psychogenic/gamepad-pmod/hardware/GamepadPMOD/GamepadPMOD.kicad_sch

## KiCad design hardware/GamepadPMOD/GamepadPMOD.kicad_sch (2026-09-07)

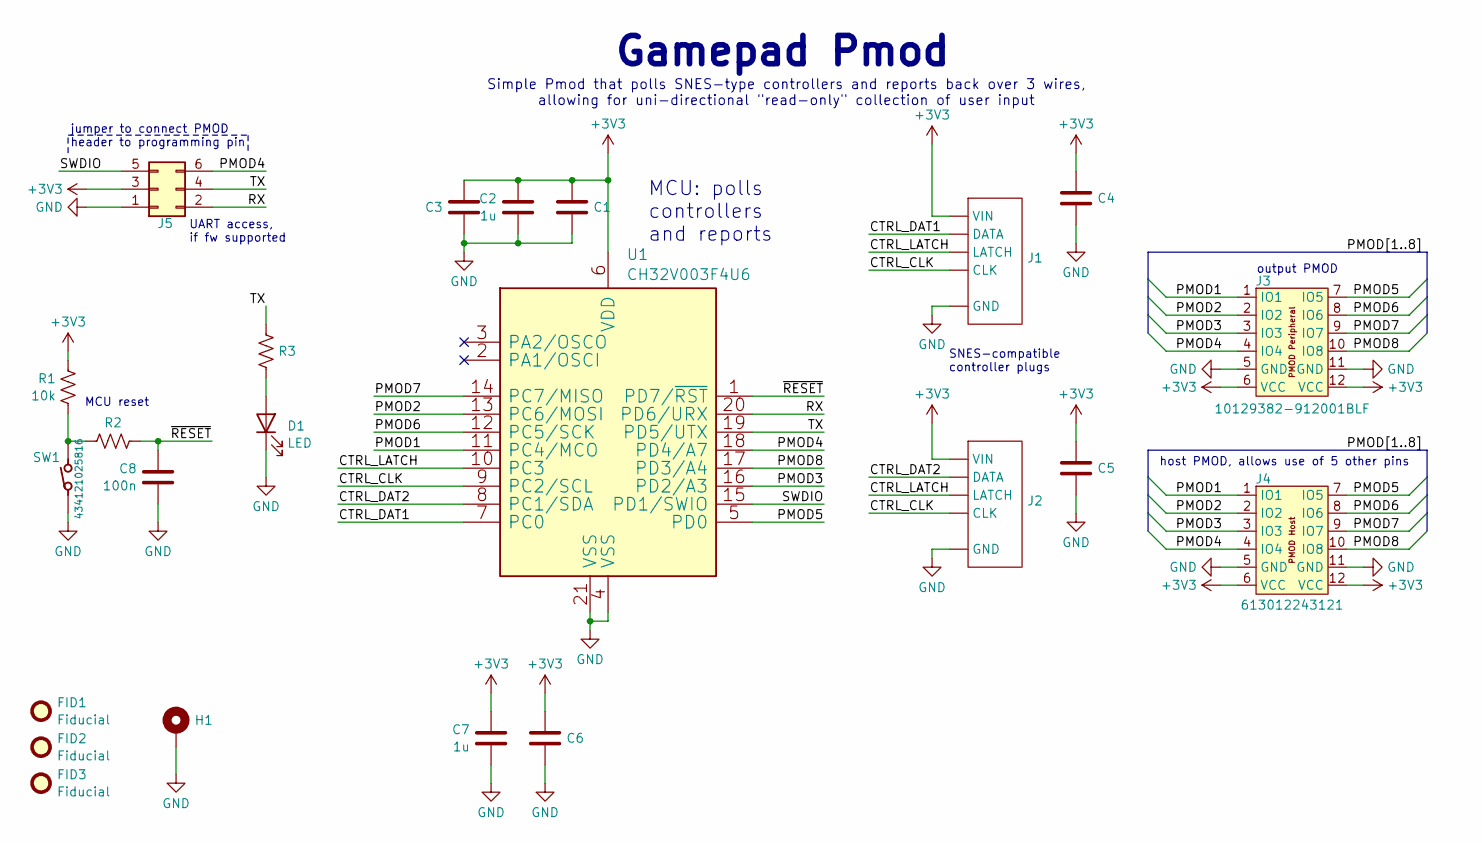
[picture p14: schematic GamepadPMOD.kicad_sch]

Parts:
C1, C4, C5, C6: C_10u_0805_35V; C_0805_2012Metric; MPN CL21A106KOQNNNE; DigikeyPN 490-10514-1-ND
C2, C7: C_1u_0603_50V; C_0603_1608Metric; MPN CL10A105KB8NNNC; DigikeyPN 490-12330-1-ND
C3, C8: C_100n_0402_50V; C_0402_1005Metric; MPN CL05B104KO5NNNC; DigikeyPN 490-13342-1-ND
D1: LED; LED_0603_1608Metric; MPN APT1608SURCK; DigikeyPN 754-1123-1-ND
FID1, FID2, FID3: Fiducial; Fiducial_1mm_Mask2mm
H1: MountingHole_Pad; MountingHole_3.2mm_M3_ISO7380_Pad
J1, J2: SFC connector VERT; snes_connector
J3: 10129382-912001BLF; PinHeader_2x06_P2.54mm_PMODPeriph2B; LCSC C492434
J4: 613012243121; PinSocket_2x06_P2.54mm_PMODHost1A; LCSC C541855
J5: Conn_02x03_Odd_Even; PinHeader_2x03_P2.54mm_Vertical; LCSC C492420
R1: R_10k_0402; R_0402_1005Metric; MPN RC0402FR-0710KL; DigikeyPN 10-ERJ-U02F1002XCT-ND
R2: R_1k_0402; R_0402_1005Metric; MPN RC0402FR-071KL; DigikeyPN A121534CT-ND
R3: 200R; R_0402_1005Metric; MPN RC0402FR-07200RL; LCSC C114764
SW1: 434121025816; MPN 434121025816; DigikeyPN 2223-TS09-63-25-R-260-SMT-TRCT-ND
U1: CH32V003F4U6; QFN-20-1EP_3x3mm_P0.4mm_EP1.65x1.65mm; MPN CH32V003F4U6; LCSC C5299908

Connections:
+3V3: C1.1, C2.1, C3.1, C4.1, C5.1, C6.1, C7.1, J1.1 (VIN), J2.1 (VIN), J3.6 (VCC), J3.12 (VCC), J4.6 (VCC), J4.12 (VCC), J5.3, R1.1, U1.6 (VDD)
CTRL_CLK: J1.2 (CLK), J2.2 (CLK), U1.9 (PC2/SCL)
CTRL_DAT1: J1.4 (DATA), U1.7 (PC0)
CTRL_DAT2: J2.4 (DATA), U1.8 (PC1/SDA)
CTRL_LATCH: J1.3 (LATCH), J2.3 (LATCH), U1.10 (PC3)
GND: C1.2, C2.2, C3.2, C4.2, C5.2, C6.2, C7.2, C8.2, D1.1 (K), H1.1, J1.7 (GND), J2.7 (GND), J3.5 (GND), J3.11 (GND), J4.5 (GND), J4.11 (GND), J5.1, SW1.1, U1.4 (VSS), U1.21 (VSS)
unnamed: D1.2 (A), R3.1
unnamed: R1.2, R2.1, SW1.2
PMOD1: J3.1 (IO1), J4.1 (IO1), U1.11 (PC4/MCO)
PMOD2: J3.2 (IO2), J4.2 (IO2), U1.13 (PC6/MOSI)
PMOD3: J3.3 (IO3), J4.3 (IO3), U1.16 (PD2/A3)
PMOD4: J3.4 (IO4), J4.4 (IO4), J5.6, U1.18 (PD4/A7)
PMOD5: J3.7 (IO5), J4.7 (IO5), U1.5 (PD0)
PMOD6: J3.8 (IO6), J4.8 (IO6), U1.12 (PC5/SCK)
PMOD7: J3.9 (IO7), J4.9 (IO7), U1.14 (PC7/MISO)
PMOD8: J3.10 (IO8), J4.10 (IO8), U1.17 (PD3/A4)
RX: J5.2, U1.20 (PD6/URX)
SWDIO: J5.5, U1.15 (PD1/SWIO)
TX: J5.4, R3.2, U1.19 (PD5/UTX)
~RESET: C8.1, R2.2, U1.1 (PD7/~RST)

Notes on the sheet:
jumper to connect PMOD header to programming pin
Gamepad Pmod
MCU reset
host PMOD, allows use of 5 other pins
SNES-compatible controller plugs
Simple Pmod that polls SNES-type controllers and reports back over 3 wires, allowing for uni-directional "read-only" collection of user input
MCU: polls controllers and reports
UART access, if fw supported
output PMOD
